gutugutu3030/realLive2d/reallive2dSimulator/data/0.png

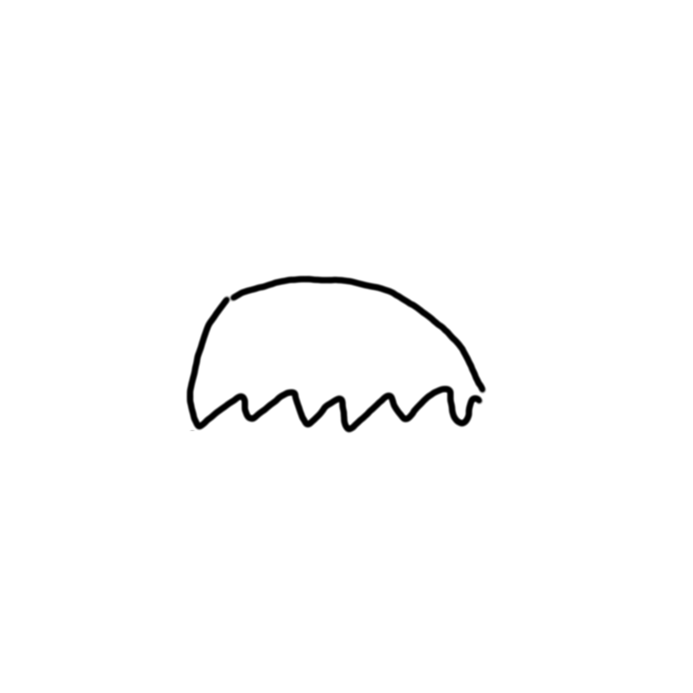
reallive2dSimulator/data/0.png
