gutugutu3030/realLive2d/reallive2dSimulator/data/2.png

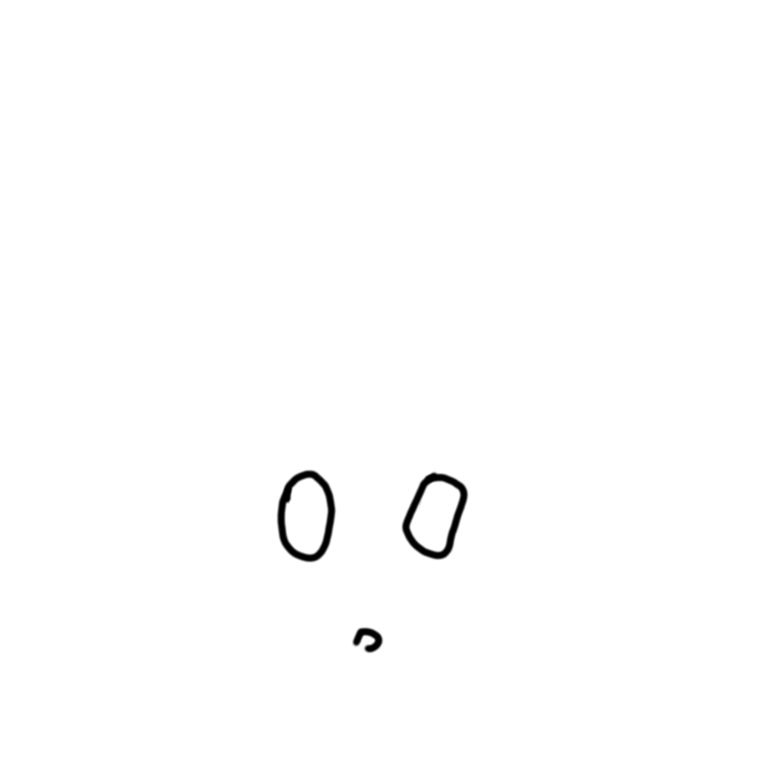
reallive2dSimulator/data/2.png
