gutugutu3030/realLive2d/reallive2dSimulator/data/-1.png

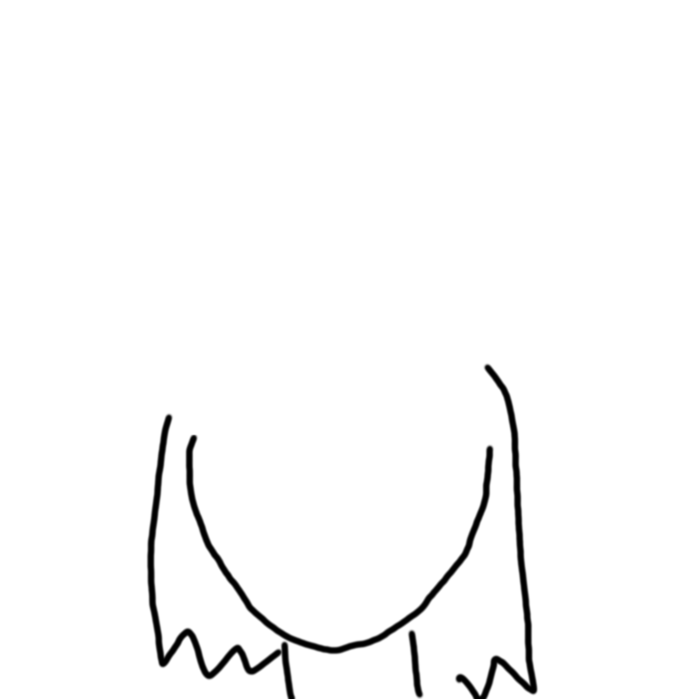
reallive2dSimulator/data/-1.png
