gutugutu3030/realLive2d/DOA.py

import sys,os
sys.path.append('usb_4_mic_array')
from tuning import Tuning
import usb.core
import usb.util
import time

dev = usb.core.find(idVendor=0x2886, idProduct=0x0018)
#print dev
if dev:
    Mic_tuning = Tuning(dev)
    print Mic_tuning.direction
    while True:
        try:
            print Mic_tuning.direction
            time.sleep(1)
        except KeyboardInterrupt:
            break
